Brezensalzer/ESP32_Web_Radio/config.h

/*
 * config.h
 * credentials
 */
 
//------------------------------------------------------------------------------
// Network
//------------------------------------------------------------------------------
// your network SSID (name)
char ssid[] = "xxx";             
// your network password
char pass[] = "xxx";   
// URL to station list
char url_stationlist[] = "http://yourhost/stationlist.txt";
