Brezensalzer/ESP32_Web_Radio/RadioStation.cpp

/*
 * RadioStation.cpp
 */

#include "RadioStation.h"

//------------------------------------------------------------------------------
// parse station list from downloaded file
//------------------------------------------------------------------------------
void StationList::parseStations(String lines)      
{
  int newlineAt, semicolonAt;
  String line;
  String label, host, path;
  numStations = 0;

  while (lines.indexOf("\n") != -1)
  {
    // find first newline
    newlineAt = lines.indexOf("\n");
    // grab line
    line = lines.substring(0, newlineAt);
    // shorten string
    lines.remove(0, newlineAt+1);

    // find first semicolon
    semicolonAt = line.indexOf(";");
    // grab field
    label = line.substring(0, semicolonAt);
    label.toCharArray(station[numStations].label, label.length()+1);
    // shorten string
    line.remove(0, semicolonAt+1);
  
    // repeat for url
    line.toCharArray(station[numStations].url, line.length()+1);    
    
    numStations++;
    if (numStations > MAXSTATIONS)
      { break; }
  }
}
